thedod/Arduino-Brain-Machine/arduino-brain-machine-mono_bb.png

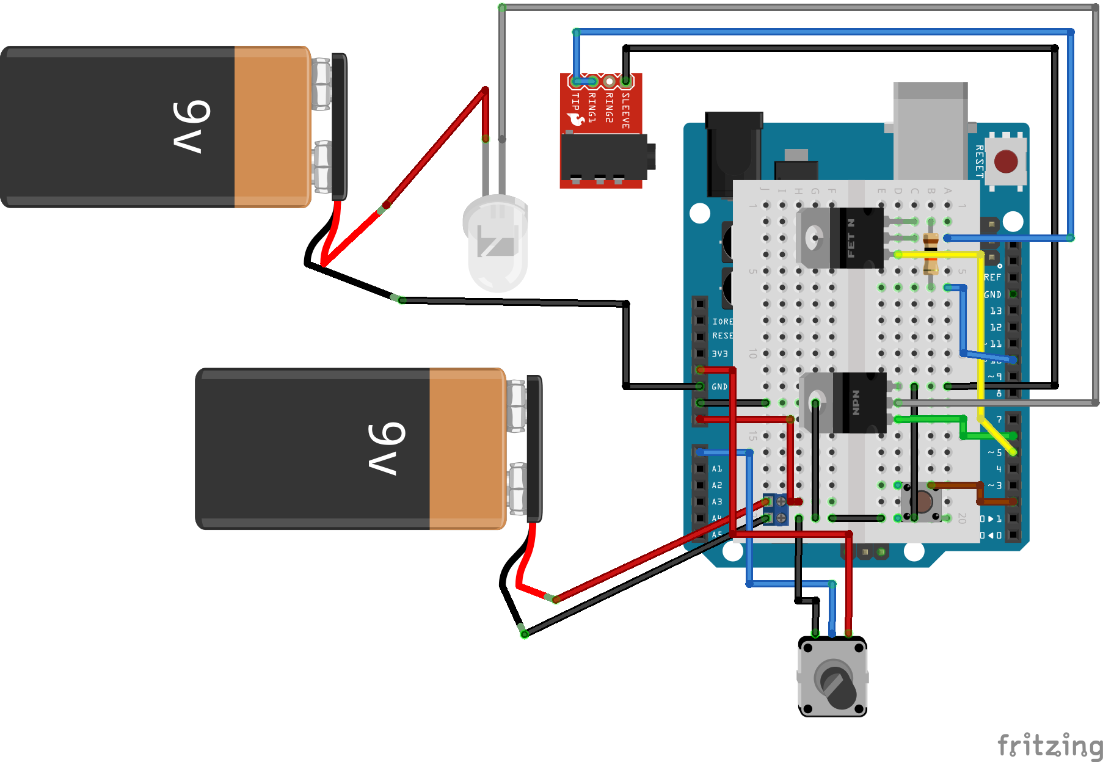
arduino-brain-machine-mono_bb.png
