thedod/Arduino-Brain-Machine/session-good-morning-proteus-04.png

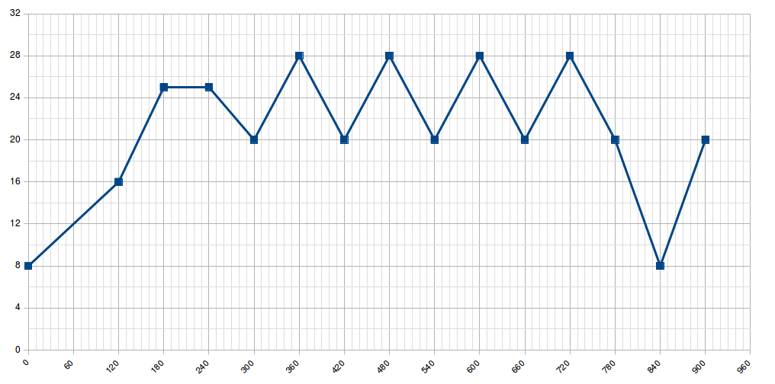
session-good-morning-proteus-04.png
