thedod/Arduino-Brain-Machine/session-good-night-proteus-43.png

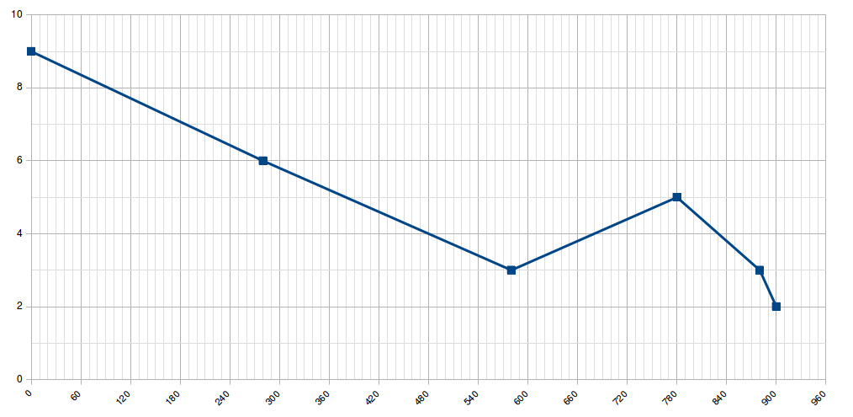
session-good-night-proteus-43.png
