thedod/Arduino-Brain-Machine/session-meditation-proteus-10.png

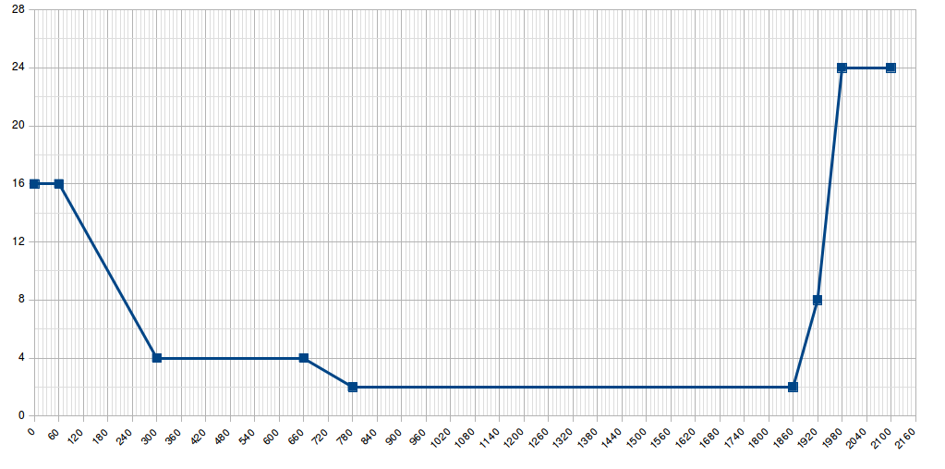
session-meditation-proteus-10.png
